Fish-in-a-Barrel/Nixie/ClockController.X/gps.c

#include <xc.h>

#include "gps.h"
#include "bcd_utils.h"
#include "time_utils.h"

/*
 * This receives and decodes the NMEA protocol RMC message sent by the GPS receiver. (§20.10)
 */

volatile struct GpsData gGpsData;

volatile static struct
{
    char time[6];
    char date[6];
    char status;
} rawGpsData;

#define STATE_AWAIT_START 0
#define STATE_CONSUME_HEADER 1
#define STATE_AWAIT_FIELD 2
#define STATE_CONSUME_FIELD 3
#define STATE_END 4

#define FIELD_TIME 0
#define FIELD_STATUS 1
#define FIELD_DATE 2
#define LAST_FIELD FIELD_DATE

volatile char* FIELD[] =
{
    rawGpsData.time,
    &(rawGpsData.status),
    rawGpsData.date
};

const uint8_t FIELD_SIZE[LAST_FIELD + 1] =
{
    sizeof(rawGpsData.time),
    sizeof(rawGpsData.status),
    sizeof(rawGpsData.date)
};

const uint8_t FIELD_OFFSET[LAST_FIELD + 1] =
{
    1, // (1) time
    1, // (2) status
    7  // (9) date
};

uint8_t gState = STATE_AWAIT_START;
uint8_t gField = FIELD_TIME;
uint8_t gCharCounter = 0;

void AwaitStart(char data)
{
    // Start character is '$'
    if ('$' == data)
    {
        gState = STATE_CONSUME_HEADER;
        gCharCounter = 0;
    }
}

void ConsumeHeader(char data)
{
    const char HEADER[] = "GPRMC";

    if (HEADER[gCharCounter++] != data)
    {
        // The header does not match the message we want.
        gState = STATE_AWAIT_START;
    }

    if (gCharCounter >= sizeof(HEADER) - 1)
    {
        // The header matches the message we want: start consuming fields;
        gState = STATE_AWAIT_FIELD;
        gField = FIELD_TIME;
        gCharCounter = 1;
    }
}

void AwaitField(char data)
{
    if ((',' == data) && (--gCharCounter == 0))
    {
        gState = STATE_CONSUME_FIELD;
    }
    else if ('*' == data)
    {
        // We have unexpectedly read the start of the checksum.
        // This would only happen if we somehow missed the start of the field. Restart to recover the state machine.
        gState = STATE_AWAIT_START;
    }
}

void AwaitNextField()
{
    if (LAST_FIELD <= gField)
    {
        gState = STATE_END;
    }
    else
    {
        gState = STATE_AWAIT_FIELD;
        ++gField;
        
        // The counter is now used to count down commas until the desired field is reached.
        gCharCounter = FIELD_OFFSET[gField];
    }
}

void ConsumeField(char data)
{
    if (',' == data)
    {
        // The field ended prematurely. The GPS probably doesn't have a fix yet.
        for (uint8_t i = 0; i < FIELD_SIZE[gField]; ++i) FIELD[gField][i] = 0;
        AwaitNextField();
    }
    else
    {
        FIELD[gField][gCharCounter++] = data;
        if (FIELD_SIZE[gField] <= gCharCounter) AwaitNextField();
    }
}

void GPS_HandleInterrupt(void)
{
    // Clear the interrupt
    PIR1bits.RC1IF = 0;
    
    // Always shift out the contents of the receive buffer.
    char data = RC1REG;

    // Toggle CREN if an overrun occurs (§24.1.2.5)
    if (RC1STAbits.OERR)
    {
        RC1STAbits.CREN = 0;
        RC1STAbits.CREN = 1;
    }

    uint8_t error = RC1STAbits.FERR;

    // Reset the state machine if there is a framing error.
    if (error)
    {
        gState = STATE_AWAIT_START;
        return;
    }

    // Run the state machine.
    switch (gState)
    {
        case STATE_AWAIT_START: AwaitStart(data); break;
        case STATE_CONSUME_HEADER: ConsumeHeader(data); break;
        case STATE_AWAIT_FIELD: AwaitField(data); break;
        case STATE_CONSUME_FIELD: ConsumeField(data); break;

        // We should never get here.
        default: AwaitStart(data);
    }

    // Handle the state machine reaching the end state.
    if (STATE_END == gState)
    {
        gGpsData.datetime.day  = BcdToBinary(rawGpsData.date + 0, 2);
        gGpsData.datetime.month = BcdToBinary(rawGpsData.date + 2, 2);
        gGpsData.datetime.year  = BcdToBinary(rawGpsData.date + 4, 2);

        gGpsData.datetime.hour   = BcdToBinary(rawGpsData.time + 0, 2);
        gGpsData.datetime.minute = BcdToBinary(rawGpsData.time + 2, 2);
        gGpsData.datetime.second = BcdToBinary(rawGpsData.time + 4, 2);

        gGpsData.status = rawGpsData.status;

        gGpsData.updated = 1;

        gState = STATE_AWAIT_START;
    }
}
