Fish-in-a-Barrel/Nixie/NixieDriver.X/pps_outputs.h

#ifndef PPS_OUTPUTS_H
#define	PPS_OUTPUTS_H

#define PPS_OUT_TMR0 0x09
#define PPS_OUT_SDA1 0x08
#define PPS_OUT_SCL1 0x07
#define PPS_OUT_SDO1 0x08
#define PPS_OUT_SCK1 0x07
#define PPS_OUT_DT1  0x06
#define PPS_OUT_TX1  0x05
#define PPS_OUT_CK1  0x05
#define PPS_OUT_PWM4 0x04
#define PPS_OUT_PWM3 0x03
#define PPS_OUT_CCP2 0x03
#define PPS_OUT_CCP1 0x02
#define PPS_OUT_LAT  0x00

#endif	/* PPS_OUTPUTS_H */
